hungggryvic/Chip-Boy/CHIP_BOY_OS_ArduinoIDE_v22_1/IronTidesApp.h

#pragma once
#include <Arduino.h>

// App lifecycle
void ironTidesEnter();   // called once when GAME is selected
void ironTidesUpdate();  // called every frame while in GAME
void ironTidesExit();    // called once when leaving GAME

// Optional helpers
bool ironTidesIsActive();
