hungggryvic/Chip-Boy/CHIP_BOY_OS_ArduinoIDE_v22_1/Microphoneapp.h

#pragma once
#include <Arduino.h>

// ============================================================================
// MICROPHONE APP
// ============================================================================

extern bool inMic;

void startMicApp();
void updateMicApp();
